dotcypress/rgb-ring/firmware/src/palette.rs

use smart_leds::RGB8;

pub fn get_color(luma: usize, temp: usize) -> RGB8 {
    PALLETE[7 - luma + temp * 8]
}

const PALLETE: [RGB8; 64] = [
    RGB8 {
        r: 165,
        g: 189,
        b: 255,
    },
    RGB8 {
        r: 128,
        g: 150,
        b: 208,
    },
    RGB8 {
        r: 96,
        g: 114,
        b: 167,
    },
    RGB8 {
        r: 70,
        g: 85,
        b: 131,
    },
    RGB8 {
        r: 48,
        g: 61,
        b: 99,
    },
    RGB8 {
        r: 31,
        g: 40,
        b: 72,
    },
    RGB8 {
        r: 17,
        g: 24,
        b: 49,
    },
    RGB8 { r: 8, g: 13, b: 31 },
    RGB8 {
        r: 176,
        g: 196,
        b: 255,
    },
    RGB8 {
        r: 138,
        g: 155,
        b: 208,
    },
    RGB8 {
        r: 106,
        g: 120,
        b: 167,
    },
    RGB8 {
        r: 78,
        g: 90,
        b: 131,
    },
    RGB8 {
        r: 55,
        g: 64,
        b: 99,
    },
    RGB8 {
        r: 35,
        g: 43,
        b: 72,
    },
    RGB8 {
        r: 21,
        g: 27,
        b: 49,
    },
    RGB8 {
        r: 10,
        g: 14,
        b: 31,
    },
    RGB8 {
        r: 191,
        g: 206,
        b: 255,
    },
    RGB8 {
        r: 151,
        g: 163,
        b: 208,
    },
    RGB8 {
        r: 117,
        g: 128,
        b: 167,
    },
    RGB8 {
        r: 88,
        g: 96,
        b: 131,
    },
    RGB8 {
        r: 63,
        g: 69,
        b: 99,
    },
    RGB8 {
        r: 42,
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
    },
    RGB8 {
        r: 131,
        g: 86,
        b: 60,
    },
    RGB8 {
        r: 99,
        g: 62,
        b: 39,
    },
    RGB8 {
        r: 72,
        g: 40,
        b: 23,
    },
    RGB8 {
        r: 49,
        g: 25,
        b: 12,
    },
    RGB8 { r: 31, g: 13, b: 5 },
];
